Retrodolivo/Power-bank/Software/Power_bank/oled_font.c

#include "oled_font.h"

const uint8_t oled_font6x8[] = 
 {
	 0x00, 0x00, 0x00, 0x00, 0x00, 0x00, // sp
	 0x00, 0x00, 0x00, 0x2f, 0x00, 0x00, // !
	 0x00, 0x00, 0x07, 0x00, 0x07, 0x00, // "
	 0x00, 0x14, 0x7f, 0x14, 0x7f, 0x14, // #
	 0x00, 0x24, 0x2a, 0x7f, 0x2a, 0x12, // $
	 0x00, 0x23, 0x13, 0x08, 0x64, 0x62, // %
	 0x00, 0x36, 0x49, 0x55, 0x22, 0x50, // &
	 0x00, 0x00, 0x05, 0x03, 0x00, 0x00, // '
	 0x00, 0x00, 0x1c, 0x22, 0x41, 0x00, // (
	 0x00, 0x00, 0x41, 0x22, 0x1c, 0x00, // )
	 0x00, 0x14, 0x08, 0x3E, 0x08, 0x14, // *
	 0x00, 0x08, 0x08, 0x3E, 0x08, 0x08, // +
	 0x00, 0x00, 0x00, 0xA0, 0x60, 0x00, // ,
	 0x00, 0x08, 0x08, 0x08, 0x08, 0x08, // -
	 0x00, 0x00, 0x60, 0x60, 0x00, 0x00, // .
	 0x00, 0x20, 0x10, 0x08, 0x04, 0x02, // /
	 0x00, 0x3E, 0x51, 0x49, 0x45, 0x3E, // 0
	 0x00, 0x00, 0x42, 0x7F, 0x40, 0x00, // 1
	 0x00, 0x42, 0x61, 0x51, 0x49, 0x46, // 2
	 0x00, 0x21, 0x41, 0x45, 0x4B, 0x31, // 3
	 0x00, 0x18, 0x14, 0x12, 0x7F, 0x10, // 4
	 0x00, 0x27, 0x45, 0x45, 0x45, 0x39, // 5
	 0x00, 0x3C, 0x4A, 0x49, 0x49, 0x30, // 6
	 0x00, 0x01, 0x71, 0x09, 0x05, 0x03, // 7
	 0x00, 0x36, 0x49, 0x49, 0x49, 0x36, // 8
	 0x00, 0x06, 0x49, 0x49, 0x29, 0x1E, // 9
	 0x00, 0x00, 0x36, 0x36, 0x00, 0x00, // :
	 0x00, 0x00, 0x56, 0x36, 0x00, 0x00, // ;
	 0x00, 0x08, 0x14, 0x22, 0x41, 0x00, // <
	 0x00, 0x14, 0x14, 0x14, 0x14, 0x14, // =
	 0x00, 0x00, 0x41, 0x22, 0x14, 0x08, // >
	 0x00, 0x02, 0x01, 0x51, 0x09, 0x06, // ?
	 0x00, 0x32, 0x49, 0x59, 0x51, 0x3E, // @
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
    0x08, 0xF8, 0x88, 0x88, 0xE8, 0x08, 0x10, 0x00, 0x20, 0x3F, 0x20, 0x00, 0x03, 0x00, 0x00, 0x00, // F 38
    0xC0, 0x30, 0x08, 0x08, 0x08, 0x38, 0x00, 0x00, 0x07, 0x18, 0x20, 0x20, 0x22, 0x1E, 0x02, 0x00, // G 39
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
	
};
