Retrodolivo/Power-bank/Software/Power_bank/RTC_DS3231.c

#include "rtc_ds3231.h"

/*Utilities*/
static uint8_t dec_to_bin(uint8_t c)
{
	uint8_t ch = ((c / 10)<<4 | c % 10);
	return ch;
}

static uint8_t bin_to_dec(uint8_t c)
{
	uint8_t ch = ((c>>4) * 10 + (0b00001111&c));
	return ch;
}
/*RTC*/
static void rtc_sqw_set(void);

void rtc_init(void)
{
	i2c_start();
	i2c_sendbyte(DS3231_WRITE_ADDR);
	i2c_sendbyte(DS3231_STATUS_ADDR);
	i2c_sendbyte(DS3231_STATUS_EN32KHZ);
	i2c_stop();	
	rtc_sqw_set();	
}

void rtc_set_time(Time_t *t, uint8_t hour, uint8_t min)
{
	i2c_start();
	i2c_sendbyte(DS3231_WRITE_ADDR);	
	i2c_sendbyte(DS3231_TIME_MIN_ADDR);
	i2c_sendbyte(dec_to_bin(t->min));
	i2c_sendbyte(dec_to_bin(t->hour));
	i2c_stop();
}

void rtc_get_time(Time_t *t)
{	
	i2c_start();
	i2c_sendbyte(DS3231_WRITE_ADDR);
	i2c_sendbyte(DS3231_TIME_CAL_ADDR);
	i2c_stop();
	i2c_start();
	i2c_sendbyte(DS3231_READ_ADDR);
	t->sec = i2c_readbyte();
	t->min = i2c_readbyte();
	t->hour = i2c_readbyte();
}

static void rtc_sqw_set(void)
{
	i2c_start();
	i2c_sendbyte(DS3231_WRITE_ADDR);
	i2c_sendbyte(DS3231_CONTROL_ADDR);
	/*Bits RS0 RS1 to LOW*/
	i2c_sendbyte(0x00);					
	i2c_stop();
}
