Retrodolivo/Power-bank/Software/Power_bank/cur_sens_acs712.h

#ifndef CUR_SENS_ACS712_H_
#define CUR_SENS_ACS712_H_

#include "main.h"

void adc_init(void);
void adc_start(void);
float acs712_get_current(void);

extern uint8_t oled_show_mode;

#define ACS712_SENSITIVITY5 0.185
#define OFFSET				0
#define VREF				5.093
#define MAX_COUNTS			100

#endif /* CUR_SENS_ACS712_H_ */
